deanm1278/tiva_motor_pack/libmotorpack/microstep_values.h

/*
 * microstep_values.h
 *
 *  Created on: May 1, 2016
 *      Author: Dean Miller
 */

#ifndef MICROSTEP_VALUES_H_
#define MICROSTEP_VALUES_H_

/* 1/256 microstepping possible with this sin table
 *
 * |	bits 0-7	|	BVREF
 * |	bits 8-15	|	AVREF
 * |	bit 16		|	BPH
 * |	bit 17		|	APH
 */

uint32_t microstep_values[1023] = {
		0x200ff,
		0x201fe,
		0x203fe,
		0x204fe,
		0x206fe,
		0x207fe,
		0x209fe,
		0x20afe,
		0x20cfe,
		0x20efe,
		0x20ffe,
		0x211fe,
		0x212fe,
		0x214fe,
		0x215fe,
		0x217fd,
		0x219fd,
		0x21afd,
		0x21cfd,
		0x21dfd,
		0x21ffd,
		0x220fc,
		0x222fc,
		0x223fc,
		0x225fc,
		0x227fb,
		0x228fb,
		0x22afb,
		0x22bfb,
		0x22dfa,
		0x22efa,
		0x230fa,
		0x231fa,
		0x233f9,
		0x234f9,
		0x236f9,
		0x237f8,
		0x239f8,
		0x23af8,
		0x23cf7,
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
};

#endif /* MICROSTEP_VALUES_H_ */
